StoicaT/.56-inch-LEDs-display-with-MAX7219/P1040263.JPG

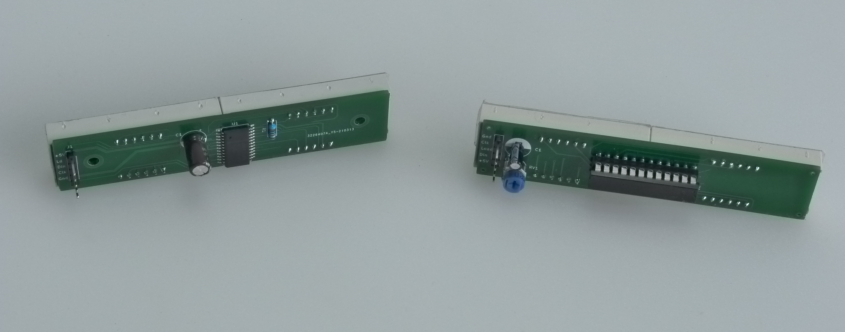
P1040263.JPG
